tfindlay-au/SerialTap/sim/rail-sag.cir

* SerialTap - rail-sag
* ===========================================================================
* QUESTION (SPDD 5.8): given a current-limited appliance rail, the board's
* bulk capacitance and the C3's WiFi transmit bursts, does the 5 V rail stay
* high enough for the buck to hold 3.3 V above the C3's brownout threshold?
*
* OUTPUT is not "it works" - it is a NUMBER: the minimum appliance source
* current this design tolerates. That number is what SPDD 12.1 step 2 goes
* and measures the Haier against.
*
* Modelled path (JST only - USB-C is not live in this deck):
*
*   VAPP -[CLIM: appliance limit]- Vsense -Rcable- Rfuse -[CLIM: eFuse]-
*        -[ideal diode]- 5V rail -+- C4 (Nichicon) -+- ceramics -+- LED
*                                 |
*                                 +- buck as a CONSTANT-POWER load -> 3V3 -> C3
*
* Sweeps the appliance current limit against how hard the radio is driven.
* See sim/README.md for how to read the results.
* ===========================================================================

.include models/behavioral.lib
.include models/pcl1a471mcl1gs.lib

* --- appliance rail (the unknown being characterised) -----------------------
.param VAPP  = 5.0      ; open-circuit service-rail voltage
.param IAPP  = 150m     ; current limit - SWEPT below; this is only a default
.param RAPP  = 0.5      ; appliance source impedance in its CV region

* --- harness and input protection --------------------------------------------
.param RCABLE = 0.25    ; ~1 m of 26 AWG, out and back
.param RFUSE  = 0.0     ; No PTC fitted: TPS2553's own limiting, thermal
+                       ; shutdown and reverse blocking make one redundant, and
+                       ; its 0.2-0.5 ohm would cost ~75 mV at 250 mA on a rail
+                       ; with no headroom (SPDD 5.3, ADR 0004)
.param IEF    = 400m    ; eFuse current limit: RILIM 66.5 kOhm, TI's 400 mA
+                       ; row; part and resistor tolerance put it at
+                       ; 351-449 mA (docs/schematic-capture.md). Was 0.60,
+                       ; stale; it must still sit clear of the transmit burst
.param RDSEF  = 0.090   ; eFuse pass resistance (TPS2553 class)

* --- 5 V rail storage ---------------------------------------------------------
* C4, PCL1A471MCL1GS 470 uF polymer: Nichicon's own 7-element model, placed by
* models/fetch-models.sh. It replaced a lumped 470 uF + 17 mOhm on 2026-09-28;
* see sim/README.md "The vendor models".
.param CCER    = 22u    ; all 5 V ceramics, DC-bias derated (SPDD 7.1)
.param ESRCER  = 5m
.param RLED    = 5k     ; power LED branch, ~1 mA

* --- buck and the load behind it ----------------------------------------------
.param VOUT     = 3.3
.param ETA      = 0.90
.param VBUCKUV  = 3.0   ; MODELLING floor: where the converter is made to stop.
+                       ; Set below any candidate part so the deck reports how
+                       ; deep a sag really goes instead of clipping at the
+                       ; threshold being judged. Readings under ~3.6 V are
+                       ; diagnostic only - regulation is already lost there.
.param VBUCKREQ = 4.0   ; REQUIREMENT: minimum input the chosen buck needs.
+                       ; PLACEHOLDER until the buck MPN is picked; `margin`
+                       ; below is simply v5min - VBUCKREQ, so results can be
+                       ; re-judged against the real number without re-running.
.param I33_RX = 0.085   ; WiFi connected, normal traffic   (SPDD 5.4)
.param I33_TX = 0.335   ; WiFi transmit peak, 20 dBm       (SPDD 5.4)

* --- radio duty ----------------------------------------------------------------
* One transmit burst of TON every TPER. TPER is stepped, so duty is
* 2 ms / TPER: 10 ms = 20%, 4 ms = 50%, 2.2 ms = 91%.
.param TON   = 2m
.param TPER  = 10m
.param TEDGE = 10u      ; PA ramp; fast, but not stiff

* --- run control ----------------------------------------------------------------
.param TSTART = 100m    ; rails settle first, then the radio starts
.param TMEAS  = 200m    ; measure only once the burst train is periodic
.param TSTOP  = 600m

* ===========================================================================
* circuit
* ===========================================================================
Vapp   app 0 {VAPP}
Xclapp app appo CLIM ILIM={IAPP} RON={RAPP}
Vsense appo jst 0                       ; what the appliance actually delivers
Rcable jst  fi  {RCABLE}
Rfuse  fi   efi {max(RFUSE,1u)}   ; guard: LTspice rejects a 0 ohm resistor.
*                                  RFUSE=0 (no PTC) becomes 1 uohm, which is
*                                  0.25 uV at 250 mA - electrically nothing.
Xefuse efi  efo CLIM ILIM={IEF} RON={RDSEF}
Dor    efo  v5  IDEALD                  ; ideal-diode OR, JST branch (FR-6)

Xbulk  v5 0 PCL1A471MCL1GS          ; C4
Xcer   v5 0 CBULKX C={CCER}  ESR={ESRCER}
Rled   v5 0 {RLED}

Vctl   ctl 0 PULSE({I33_RX} {I33_TX} {TSTART} {TEDGE} {TEDGE} {TON} {TPER})
Xbuck  v5 0 ctl BUCKLOAD VOUT={VOUT} ETA={ETA} VUV={VBUCKUV}

* ===========================================================================
* sweeps
*   IAPP  what the appliance can supply - the unknown being bracketed
*   TPER  how hard the radio is driven:
*           10m   20% duty - steady ESPHome traffic
*            4m   50% duty - busy link
*          2.2m   91% duty - association / OTA. Effectively sustained
*                 transmit: the case bulk capacitance CANNOT ride out,
*                 and the condition SPDD 12.1 step 8 insists on testing.
* ===========================================================================
.step param IAPP list 50m 75m 100m 110m 120m 130m 150m 175m 200m 225m 250m 275m 300m
.step param TPER list 10m 4m 2.2m

.tran 0 {TSTOP} 0 20u
.options plotwinsize=0 method=gear
* Gear, not LTspice's default modified trapezoidal: C4's vendor model puts
* 3.1 nH in series with 6.6 mOhm, a ~0.5 ns time constant against a 10-20 us
* step. Under trap that stiffness made isolated steps return all-zero
* measurements with no error logged (2026-09-28: IAPP=250m at 20% duty). Gear
* removes them; elsewhere it moves v5min by under 0.3 mV.
.save V(v5) V(jst) V(ctl) I(Vsense)

.meas TRAN v5min    MIN V(v5)     FROM {TMEAS} TO {TSTOP}
.meas TRAN v5avg    AVG V(v5)     FROM {TMEAS} TO {TSTOP}
.meas TRAN iapp_avg AVG I(Vsense) FROM {TMEAS} TO {TSTOP}
.meas TRAN iapp_pk  MAX I(Vsense) FROM {TMEAS} TO {TSTOP}
.meas TRAN margin   PARAM v5min-{VBUCKREQ}
.end
